markreds81/clima-node/Button.cpp

/************************************************************************************
 * 
 * Name    : mrButton
 * File    : Button.cpp
 * Author  : Mark Reds <marco@markreds.it>
 * Date    : December 7, 2020
 * Version : 1.0.0
 * Notes   : Arduino library to drive a push button.
 * 
 * Copyright (C) 2020 Marco Rossi (aka Mark Reds).  All right reserved.
 * 
 * This file is part of mrButton.
 *
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
 ************************************************************************************/

#include "Button.h"

Button::Button(const uint8_t pin) :
	m_pin(pin),
	m_state(HIGH),
	m_changed(false),
	m_delay(500),
	m_timer(0) {
	
}

Button::~Button() {

}

bool Button::read() {
	uint32_t timer = millis();
	if (timer > m_timer && digitalRead(m_pin) != m_state) {
		m_timer = timer + m_delay;
		m_state = !m_state;
		m_changed = true;
	}
	return m_state;
}

bool Button::changed() {
	if (m_changed) {
		m_changed = false;
		return true;
	}
	return false;
}

bool Button::toggled() {
	read();
	return changed();
}
